omarmustafa130/UVC-Disinfection/Screenshots/Bottom3D_1.png

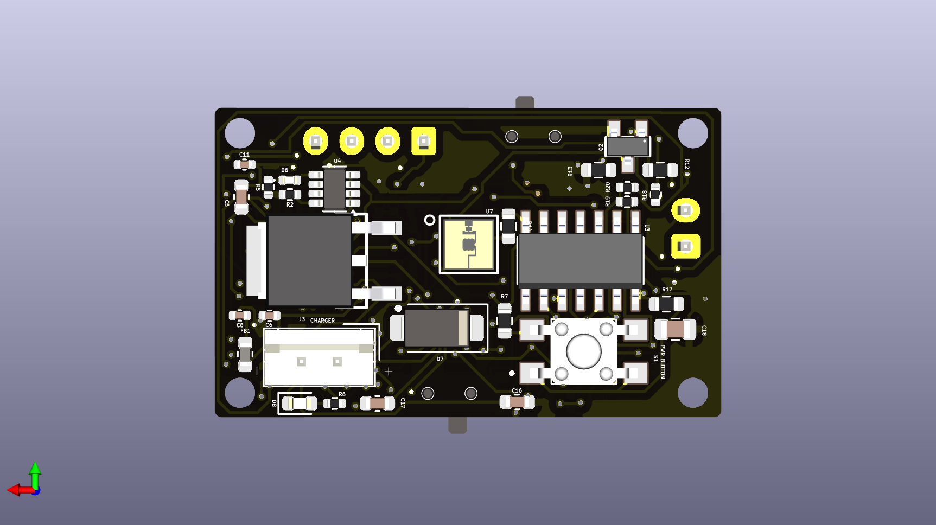
Screenshots/Bottom3D_1.png
