omarmustafa130/UVC-Disinfection/Screenshots/bottom layer.png

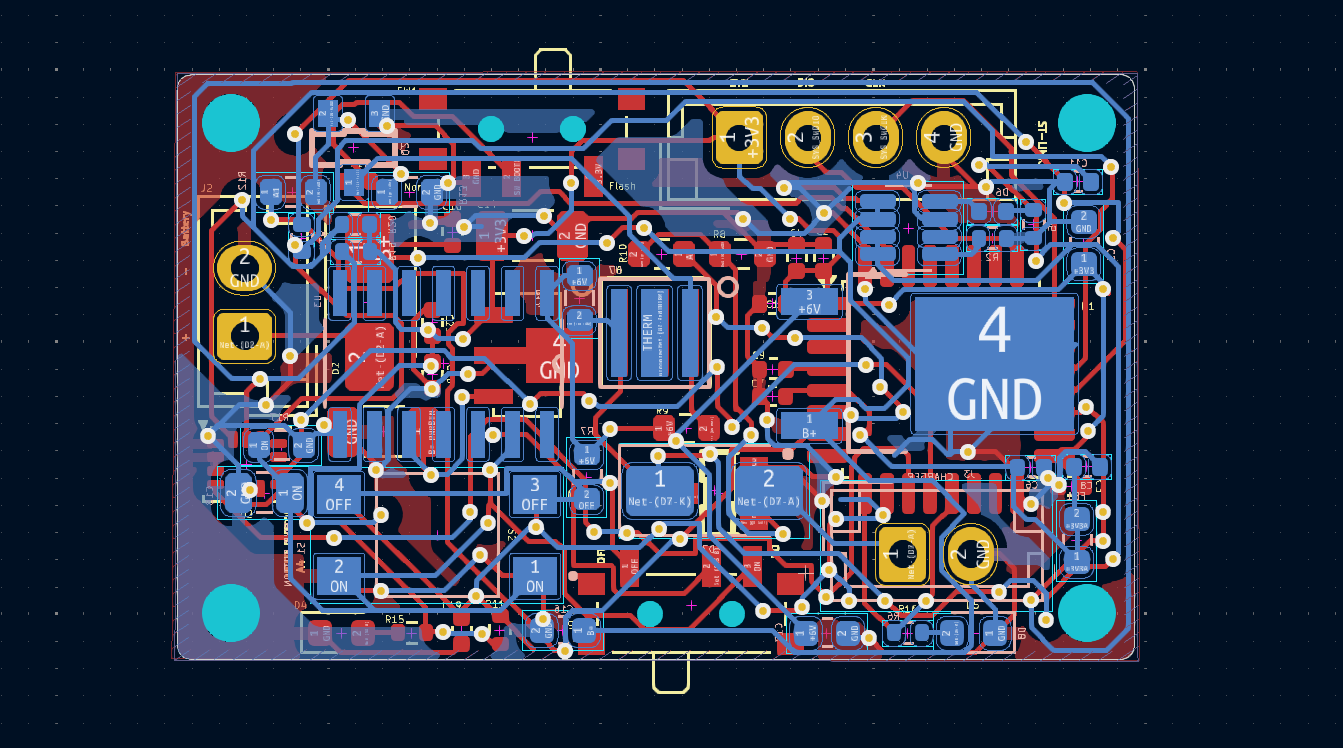
Screenshots/bottom layer.png
