omarmustafa130/UVC-Disinfection/Screenshots/top layer.png

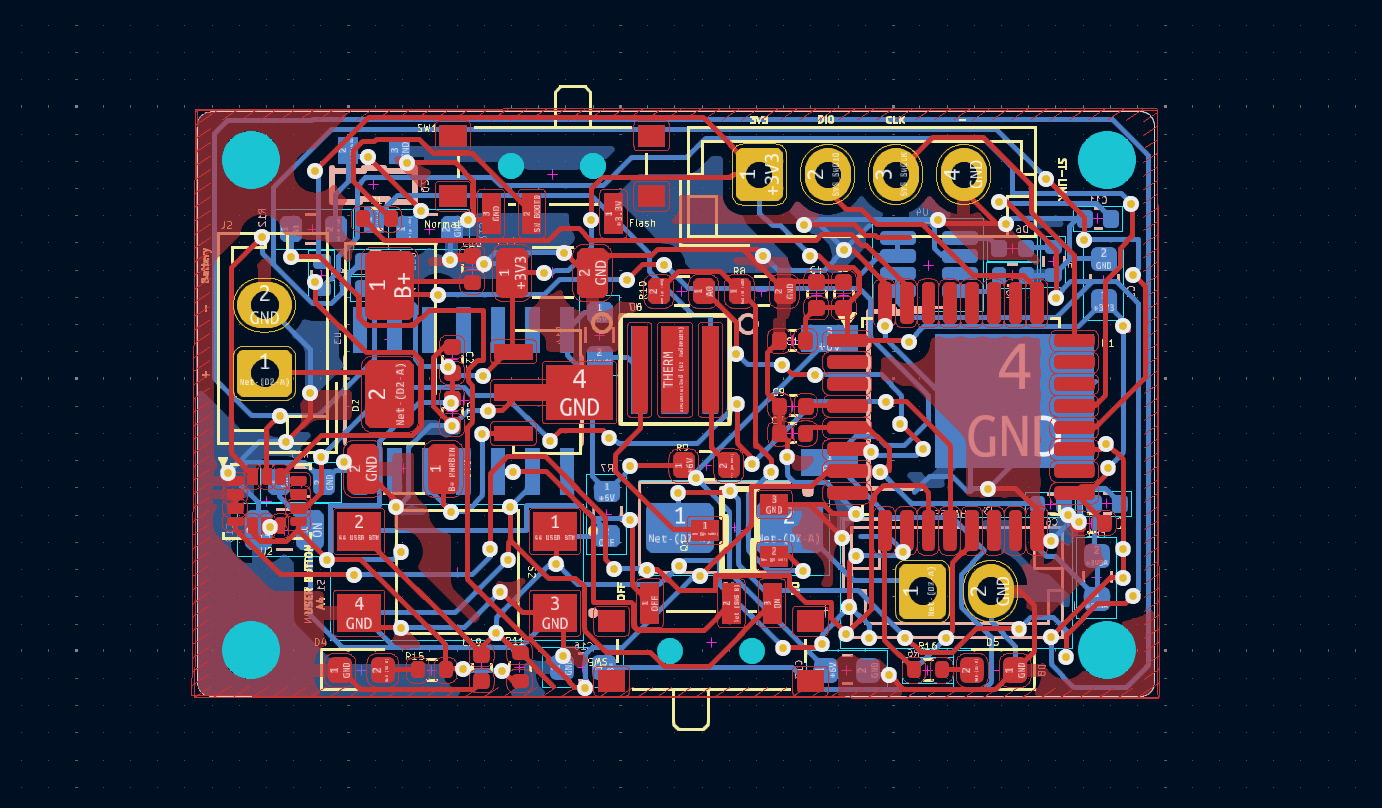
Screenshots/top layer.png
